fussdeek-del/N-X-H-desktop-Hud/ASSETS/case side.png

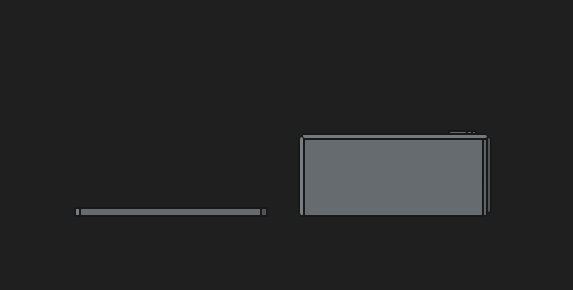
ASSETS/case side.png
