fussdeek-del/N-X-H-desktop-Hud/APP/hud_app/hud-app/config.py

UPDATE_INTERVAL_MS = 1000
WINDOW_TITLE = "HUD Monitor"
MAIN_DRIVE = None
SINGLE_INSTANCE_NAME = "HUDMonitorSingleInstance"
SERIAL_PORT = None
SERIAL_BAUDRATE = 115200
SERIAL_RETRY_SECONDS = 3

BG_COLOR = "#0f1319"
GRAPH_BG = "#131a22"
TEXT_COLOR = "#e8edf5"
ACCENT_COLOR = "#1d2633"
CARD_BG = "#151c25"
MUTED_TEXT = "#97a3b7"
WINDOW_SIZE = "420x360"

GRAPH_WIDTH = 250
GRAPH_HEIGHT = 42
GRAPH_POINTS = 40
MAX_VISIBLE_METRICS = 4
